septentrio-gnss/mosaicHAT/doc_resources/antenna_jumper.png

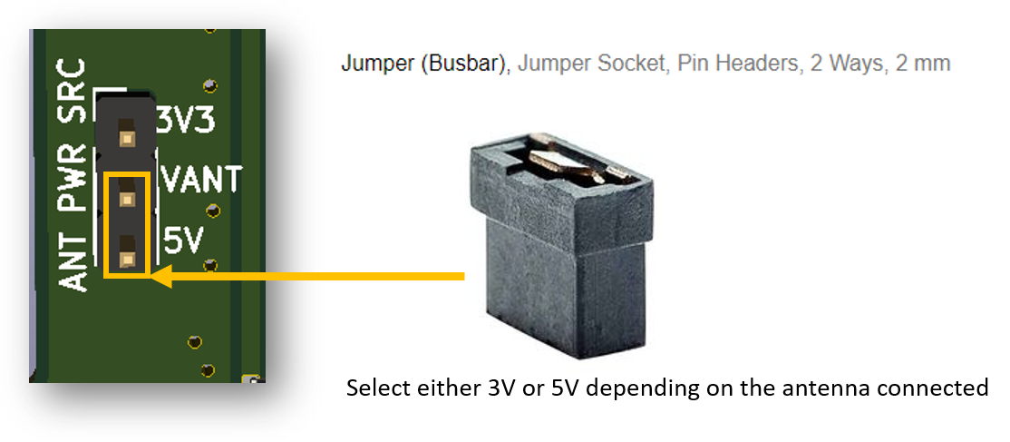
doc_resources/antenna_jumper.png
