septentrio-gnss/mosaicHAT/doc_resources/boardimage.jpg

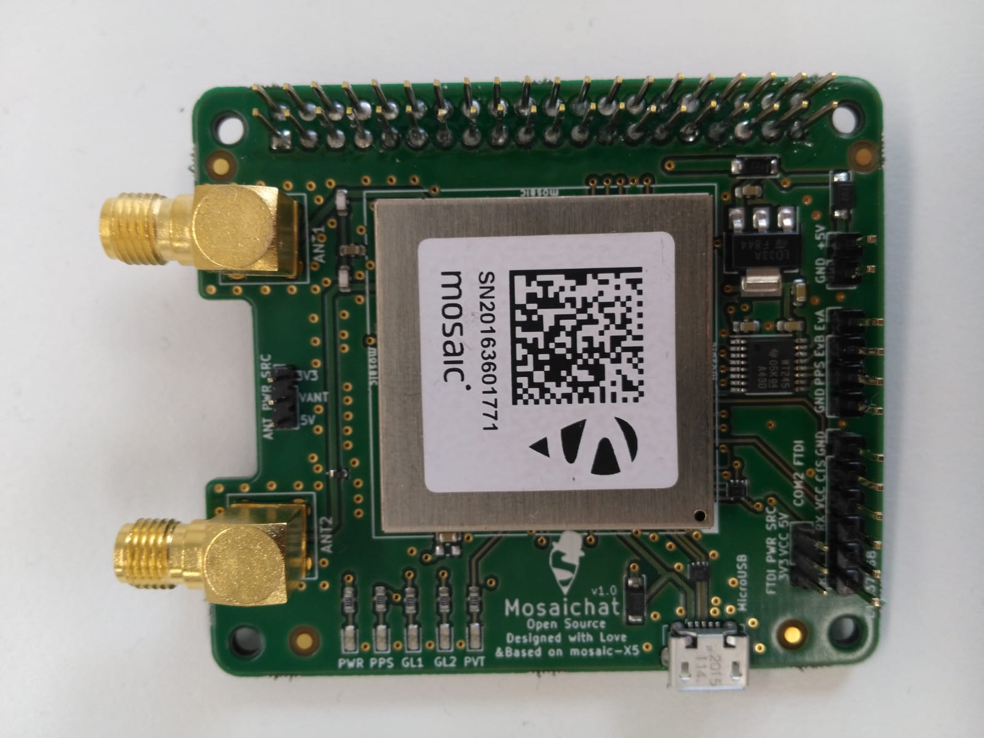
doc_resources/boardimage.jpg
