septentrio-gnss/mosaicHAT/doc_resources/deadsea_yt.png

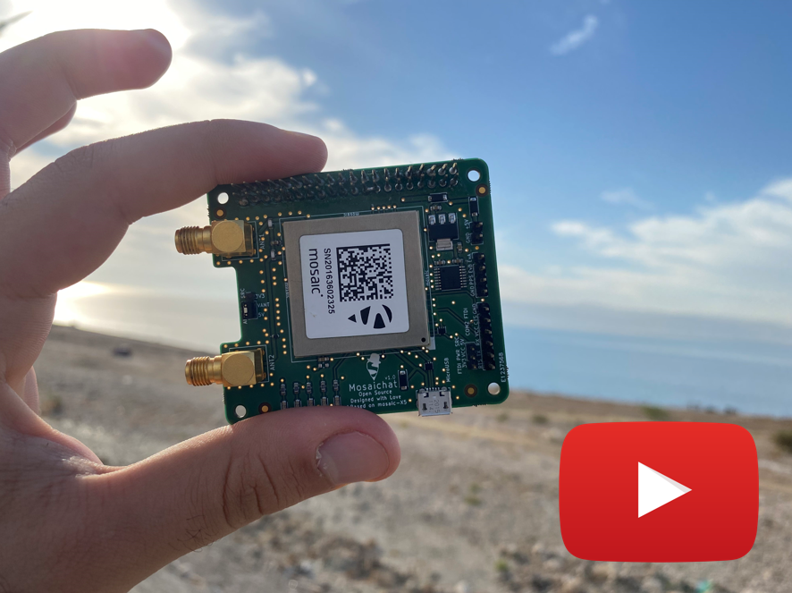
doc_resources/deadsea_yt.png
