septentrio-gnss/mosaicHAT/doc_resources/enable_serial_1.png

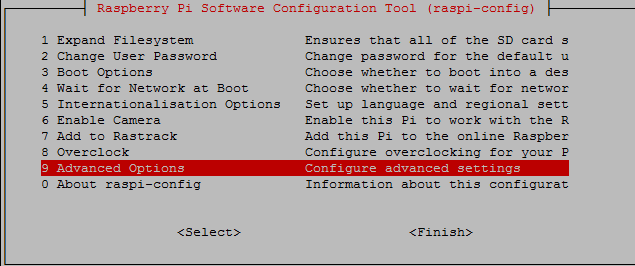
doc_resources/enable_serial_1.png
