septentrio-gnss/mosaicHAT/doc_resources/leds.png

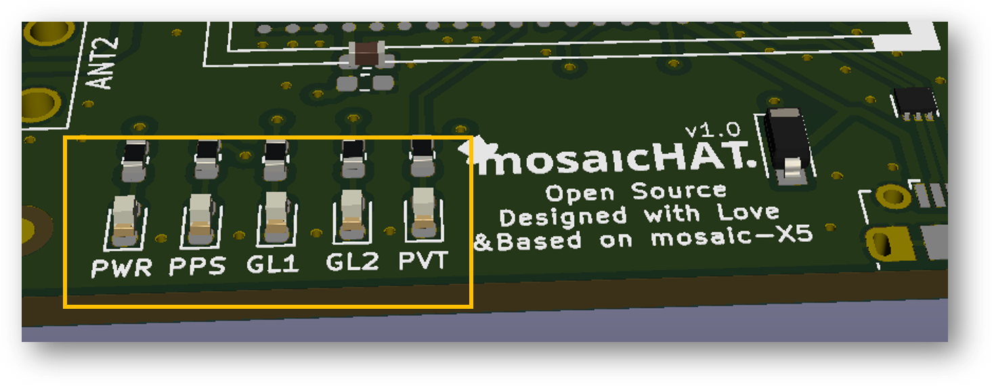
doc_resources/leds.png
