septentrio-gnss/mosaicHAT/doc_resources/mosaicHAT_noborder_noundertext.png

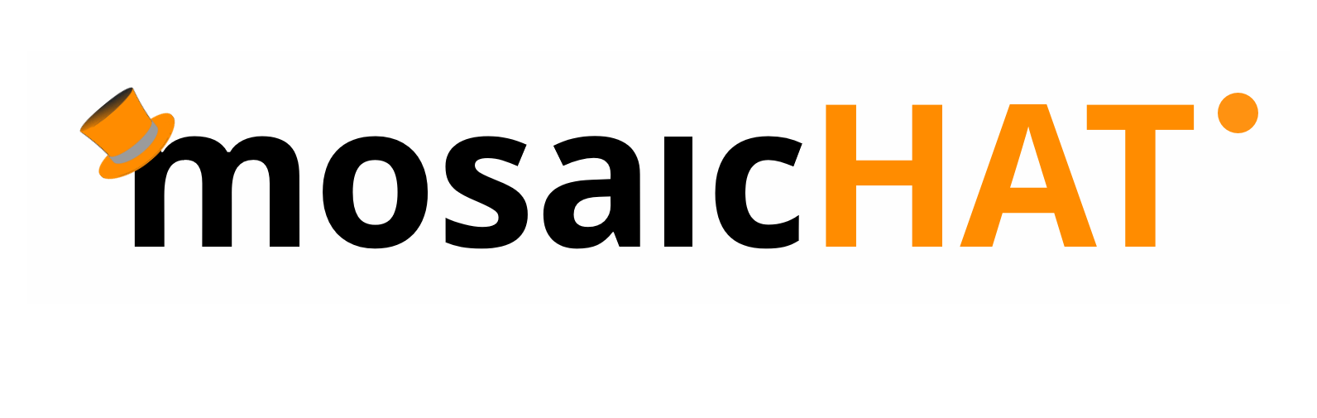
doc_resources/mosaicHAT_noborder_noundertext.png
