septentrio-gnss/mosaicHAT/doc_resources/rpi_connector.PNG

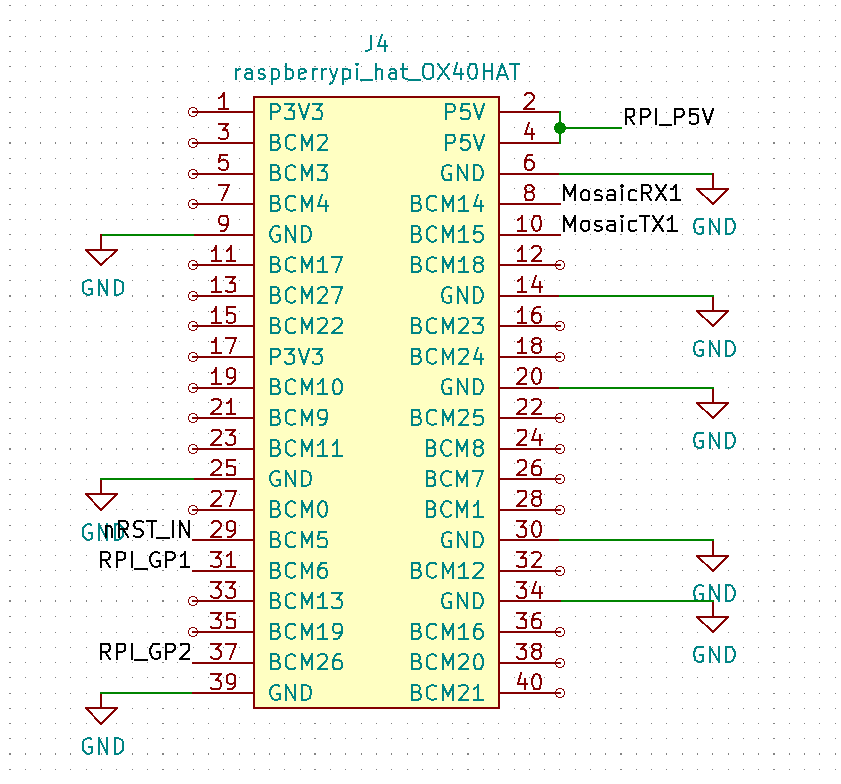
doc_resources/rpi_connector.PNG
