septentrio-gnss/mosaicHAT/doc_resources/yt_jamal.PNG

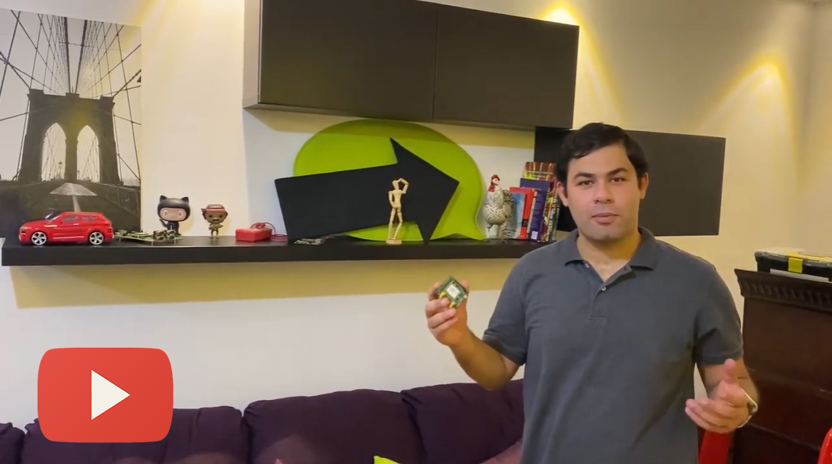
doc_resources/yt_jamal.PNG
